dfigueroa11/bibliotecas_autoprestamo_UNAL/carcasa final/Caja 1.0/Captura de pantalla 2022-06-06 223202.png

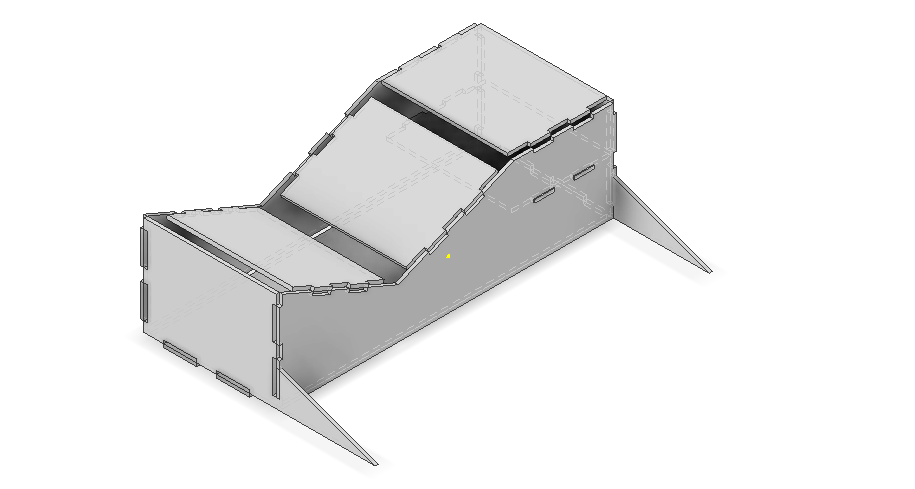
carcasa final/Caja 1.0/Captura de pantalla 2022-06-06 223202.png
