dfigueroa11/bibliotecas_autoprestamo_UNAL/images/autenticación.PNG

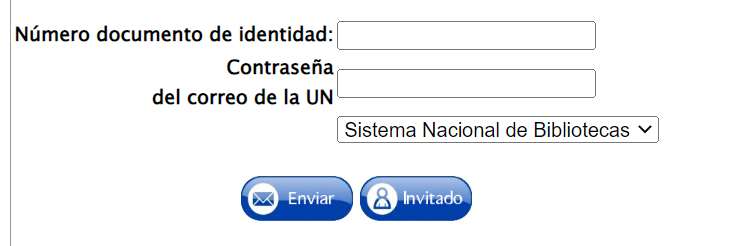
images/autenticación.PNG
