dfigueroa11/bibliotecas_autoprestamo_UNAL/images/autoprestamo.PNG

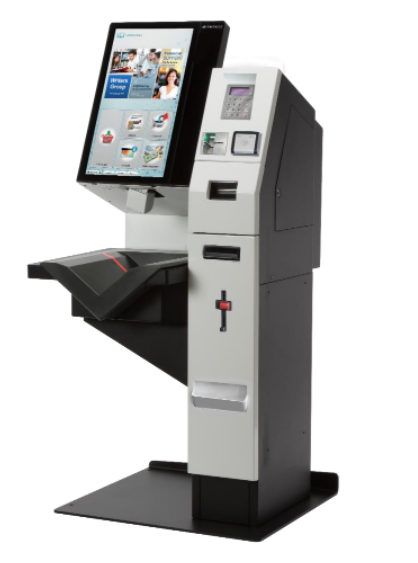
images/autoprestamo.PNG
