dfigueroa11/bibliotecas_autoprestamo_UNAL/images/biblioteca.PNG

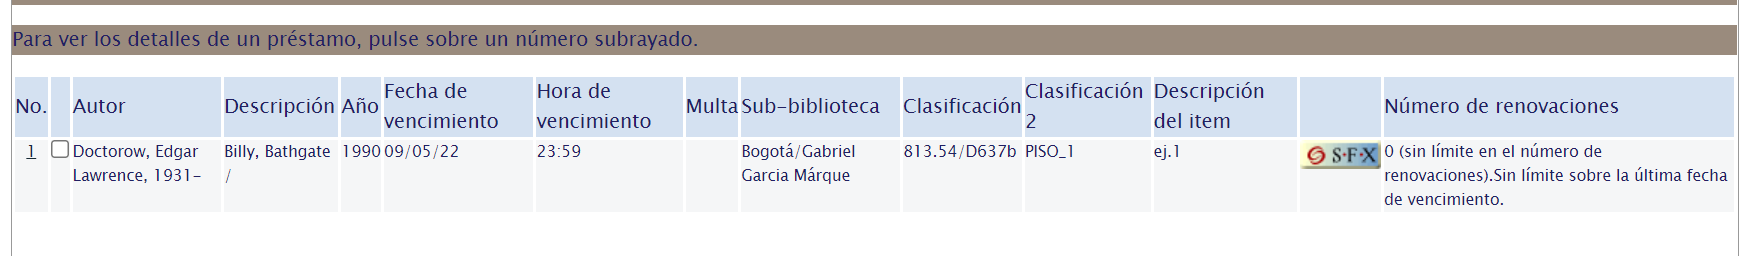
images/biblioteca.PNG
