dfigueroa11/bibliotecas_autoprestamo_UNAL/images/bibliotecas1.jpg

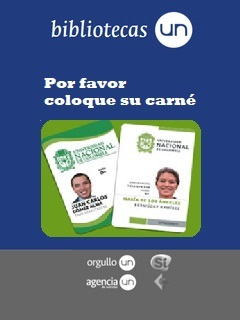
images/bibliotecas1.jpg
