dfigueroa11/bibliotecas_autoprestamo_UNAL/images/bibliotecas2.jpg

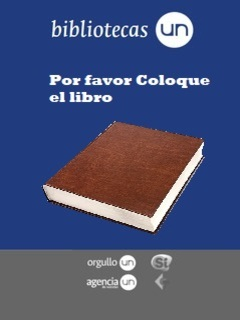
images/bibliotecas2.jpg
