dfigueroa11/bibliotecas_autoprestamo_UNAL/images/bibliotecas3.jpg

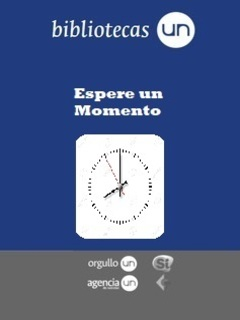
images/bibliotecas3.jpg
