dfigueroa11/bibliotecas_autoprestamo_UNAL/images/bibliotecas4.jpg

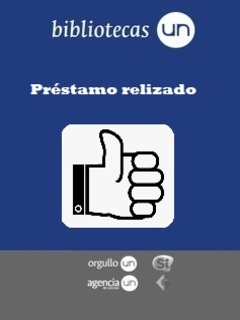
images/bibliotecas4.jpg
