dfigueroa11/bibliotecas_autoprestamo_UNAL/images/carcasa1.jpeg

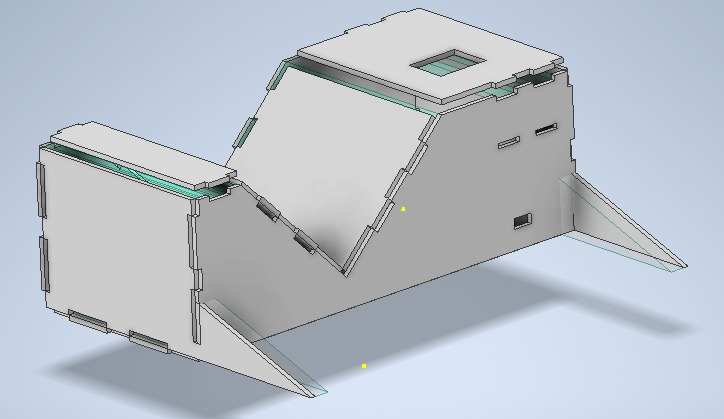
images/carcasa1.jpeg
