dfigueroa11/bibliotecas_autoprestamo_UNAL/images/diagrama_bloques.png

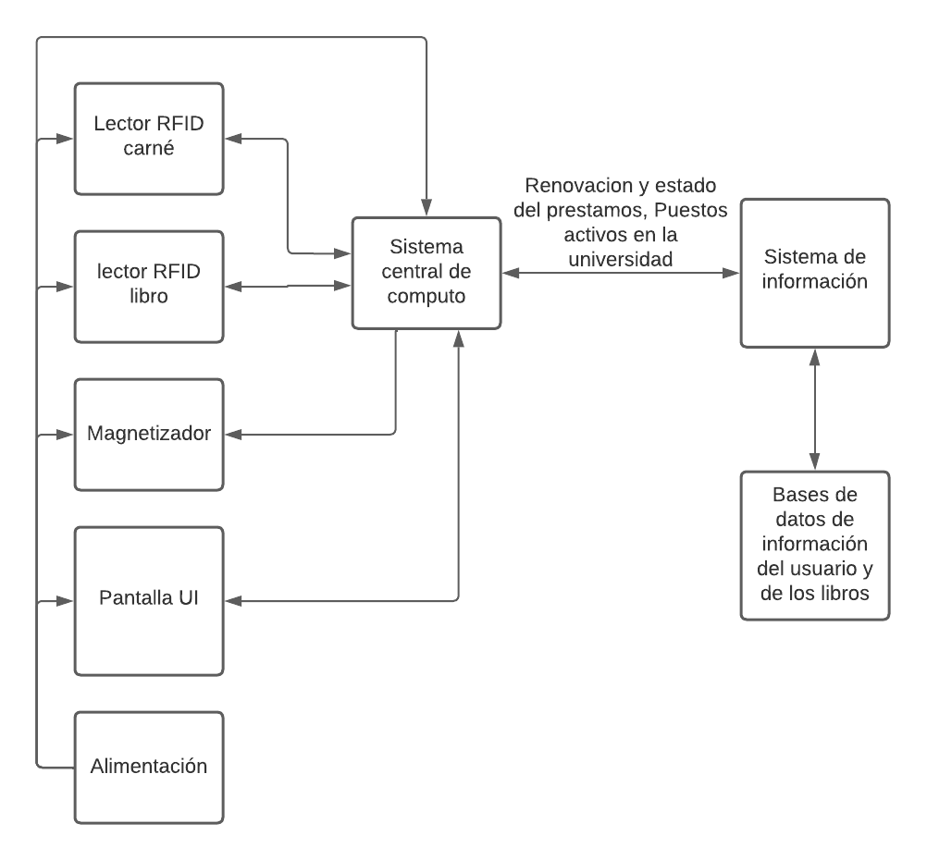
images/diagrama_bloques.png
