dfigueroa11/bibliotecas_autoprestamo_UNAL/images/diagrama_conexiones.png

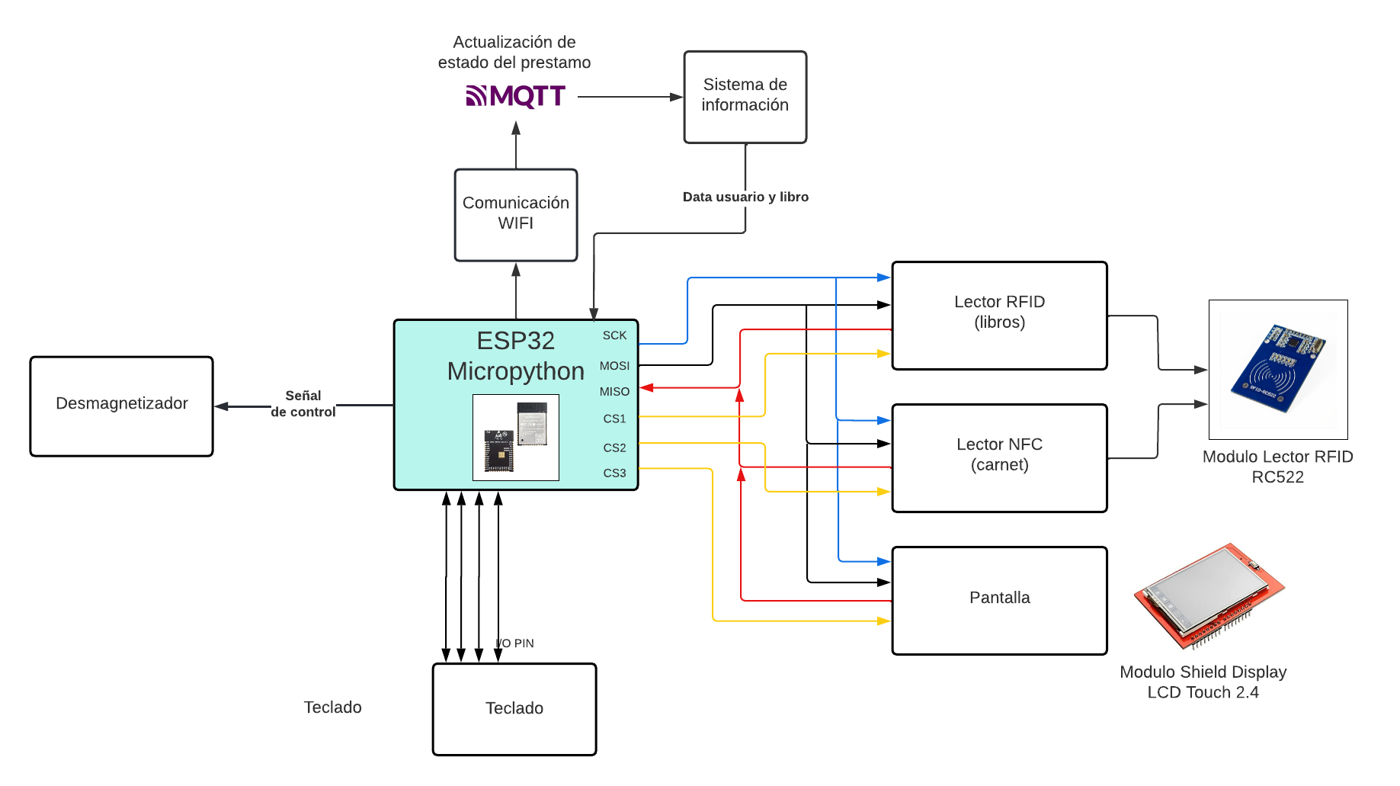
images/diagrama_conexiones.png
