dfigueroa11/bibliotecas_autoprestamo_UNAL/images/diagrama_de_software.jpg

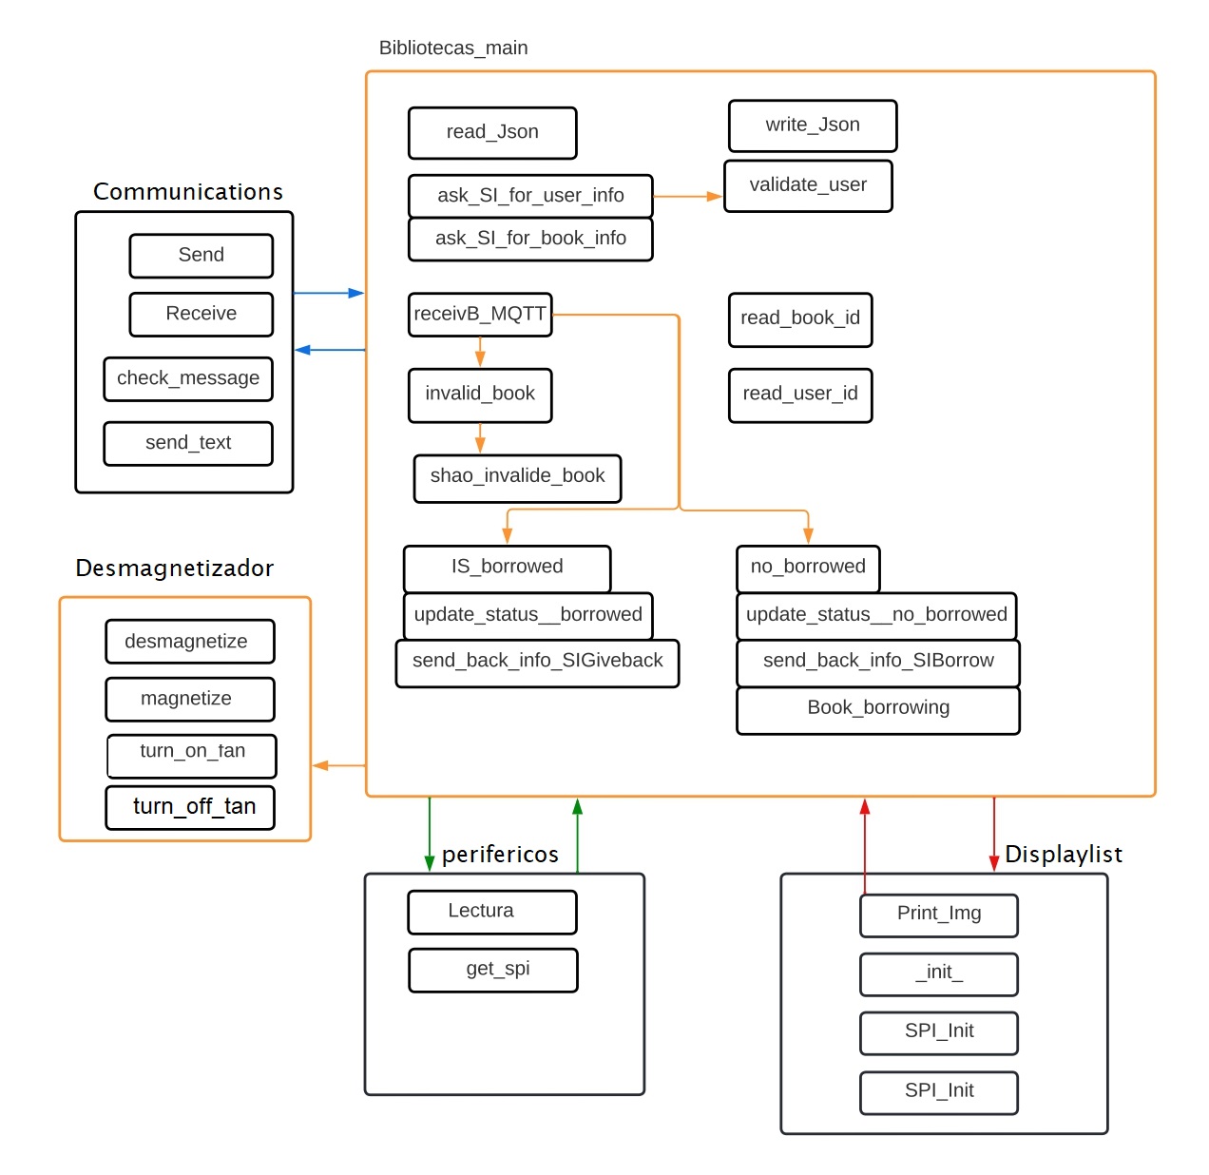
images/diagrama_de_software.jpg
