dfigueroa11/bibliotecas_autoprestamo_UNAL/images/ejemplo_bobinas_desmagnetizador.png

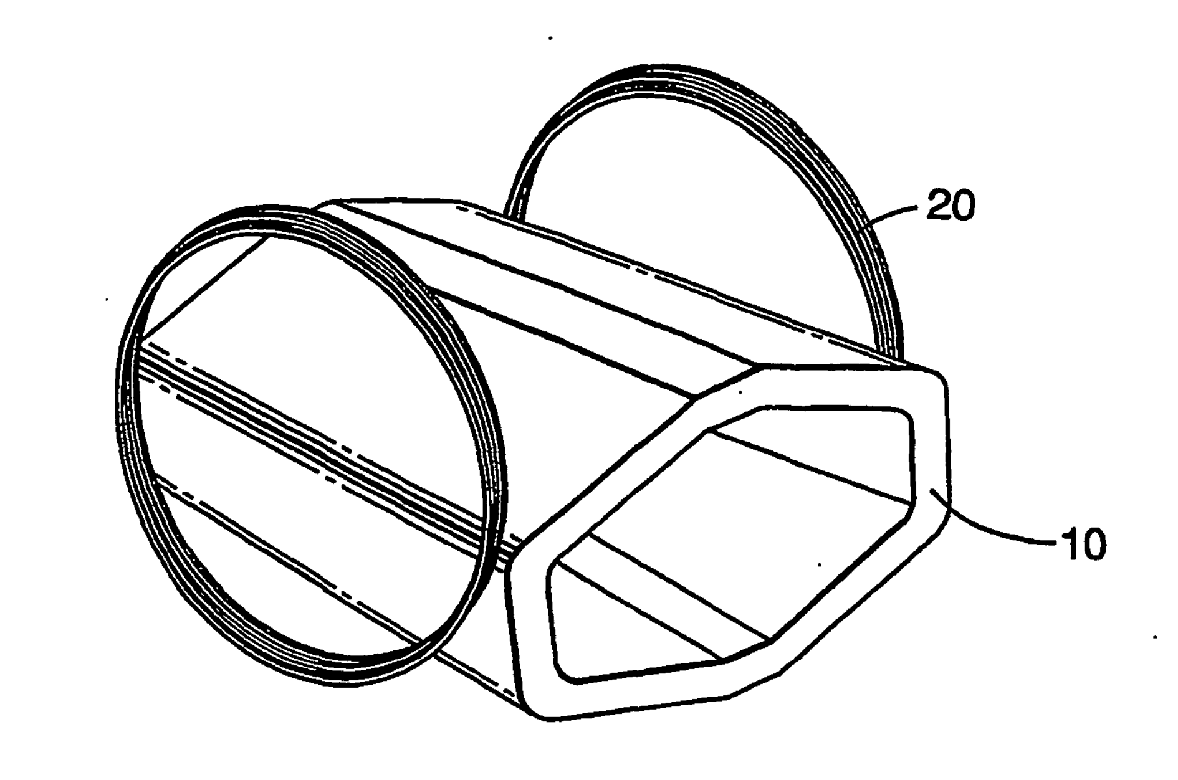
images/ejemplo_bobinas_desmagnetizador.png
