dfigueroa11/bibliotecas_autoprestamo_UNAL/images/ejemplo_circuito_desmagnetizador.png

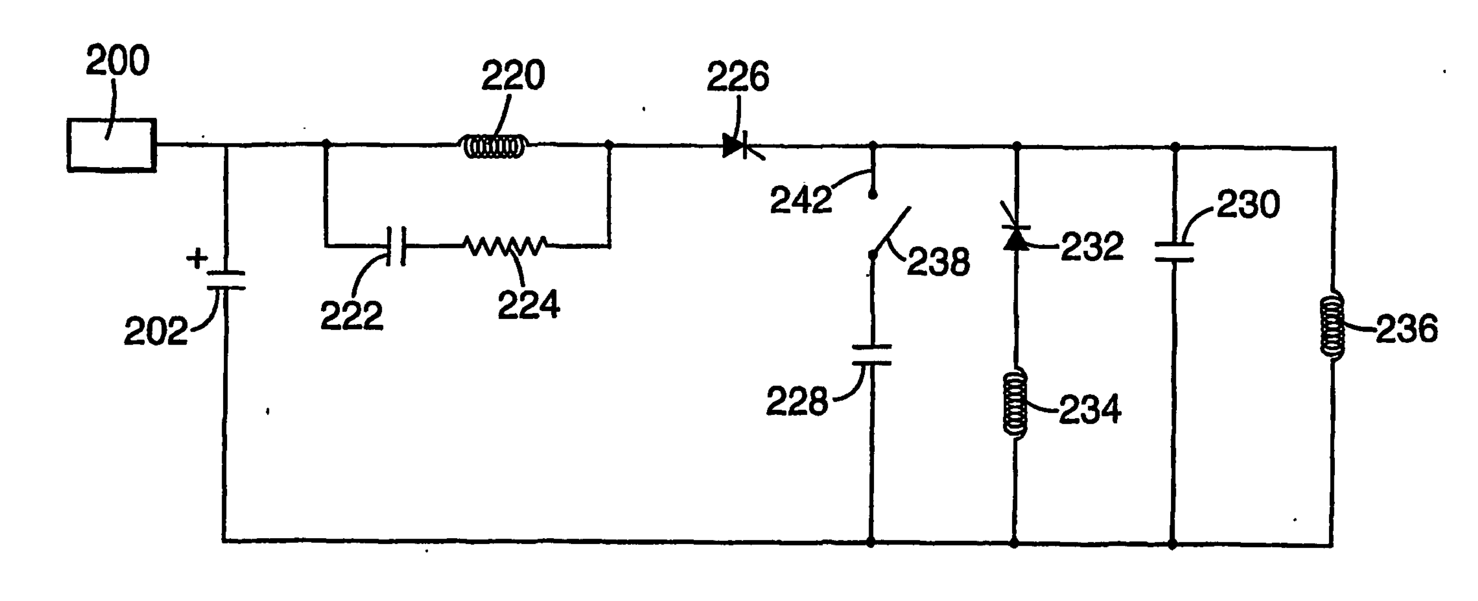
images/ejemplo_circuito_desmagnetizador.png
