dfigueroa11/bibliotecas_autoprestamo_UNAL/images/esquema.PNG

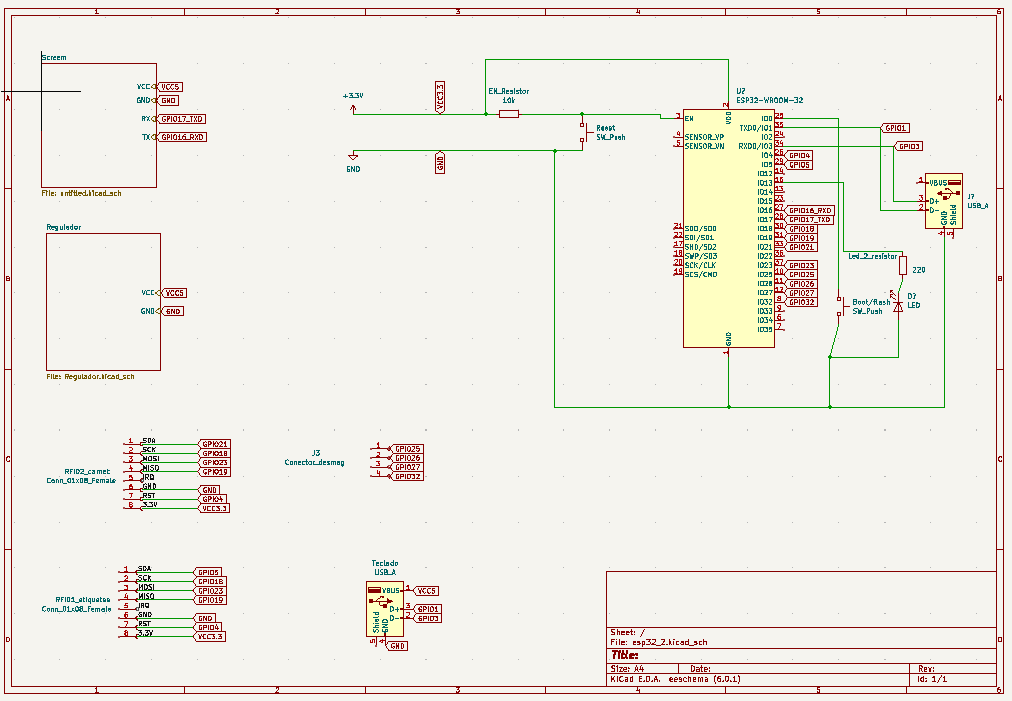
images/esquema.PNG
