dfigueroa11/bibliotecas_autoprestamo_UNAL/images/esquema_esp.PNG

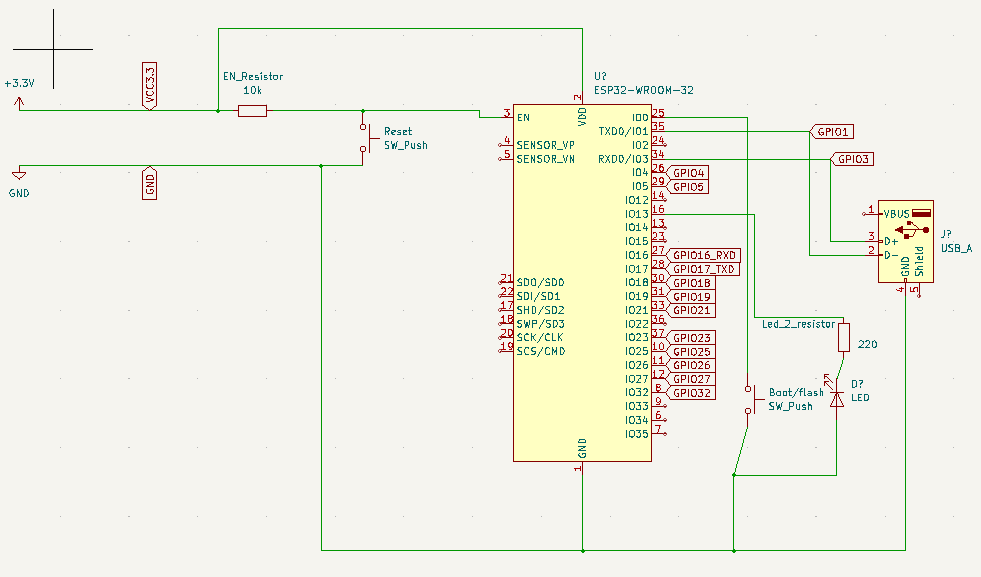
images/esquema_esp.PNG
