dfigueroa11/bibliotecas_autoprestamo_UNAL/images/esquema_fuente.PNG

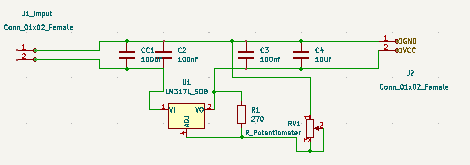
images/esquema_fuente.PNG
