dfigueroa11/bibliotecas_autoprestamo_UNAL/images/esquema_pantalla.PNG

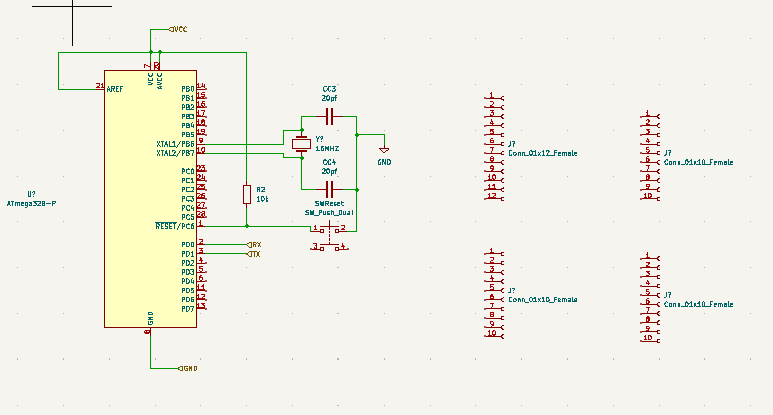
images/esquema_pantalla.PNG
