dfigueroa11/bibliotecas_autoprestamo_UNAL/images/esquema_serial.PNG

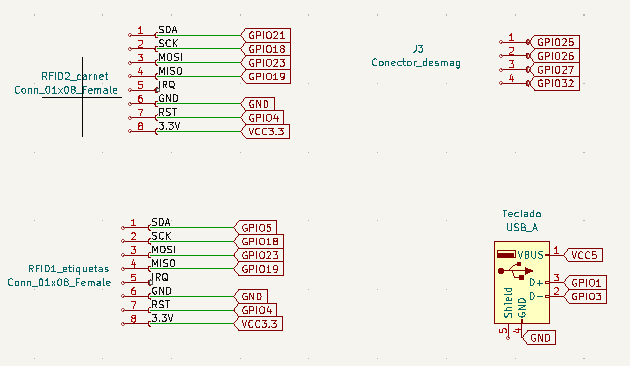
images/esquema_serial.PNG
