dfigueroa11/bibliotecas_autoprestamo_UNAL/images/flujo_bibliotecas.png

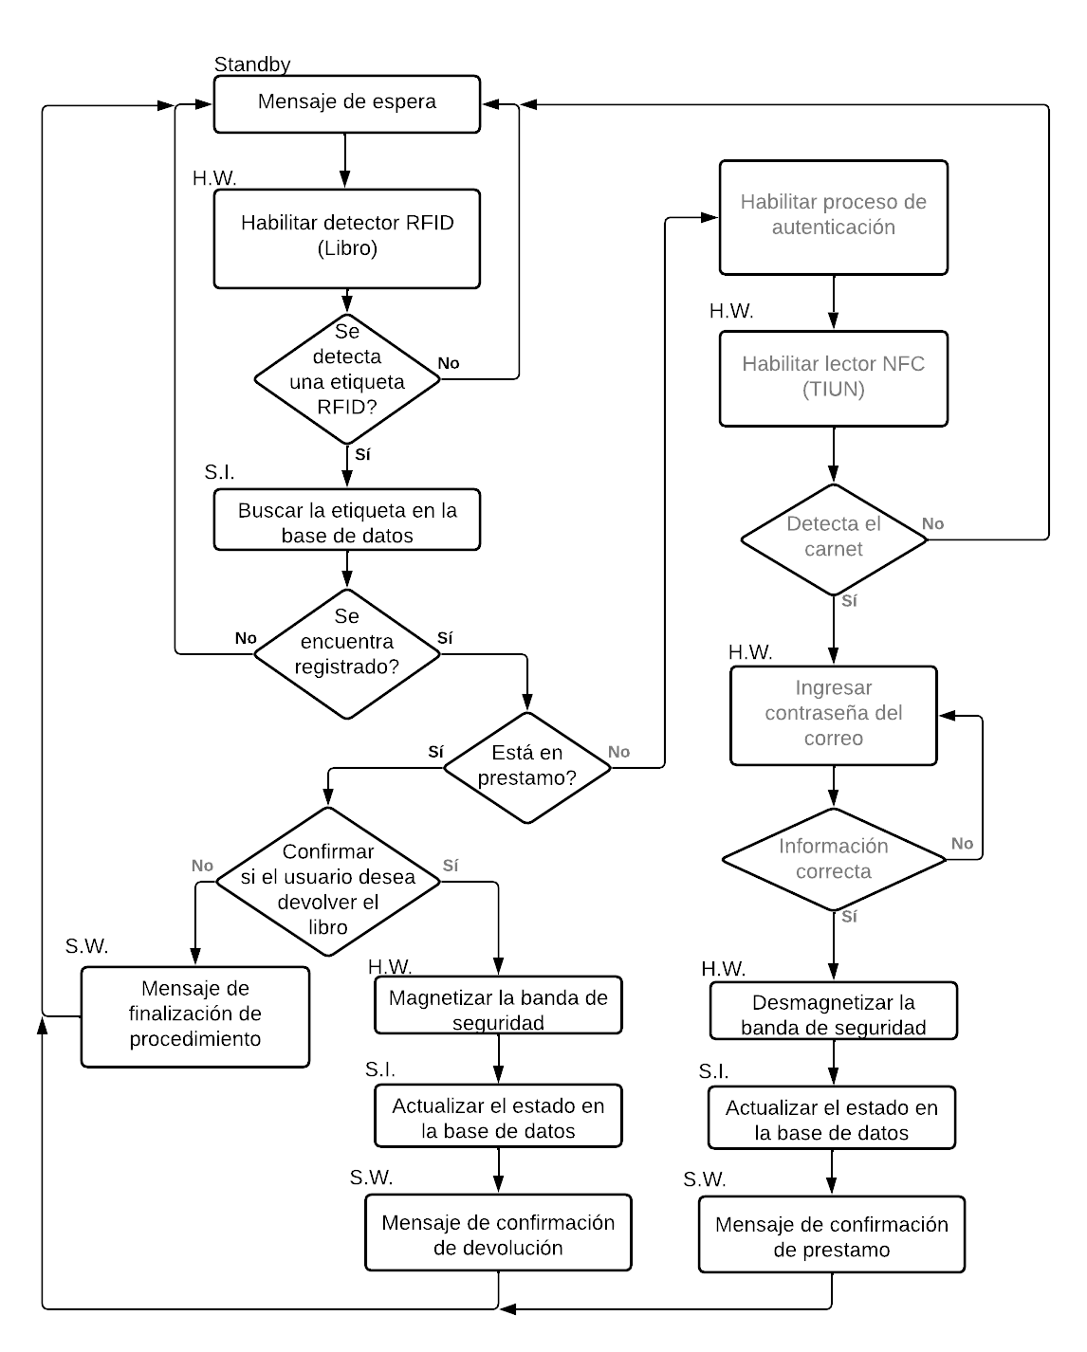
images/flujo_bibliotecas.png
