dfigueroa11/bibliotecas_autoprestamo_UNAL/images/ili9341.jpg

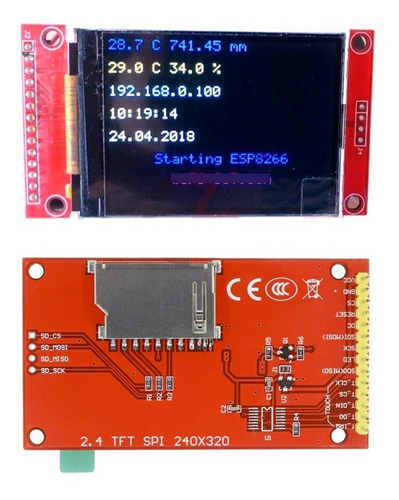
images/ili9341.jpg
