dfigueroa11/bibliotecas_autoprestamo_UNAL/images/keypad.PNG

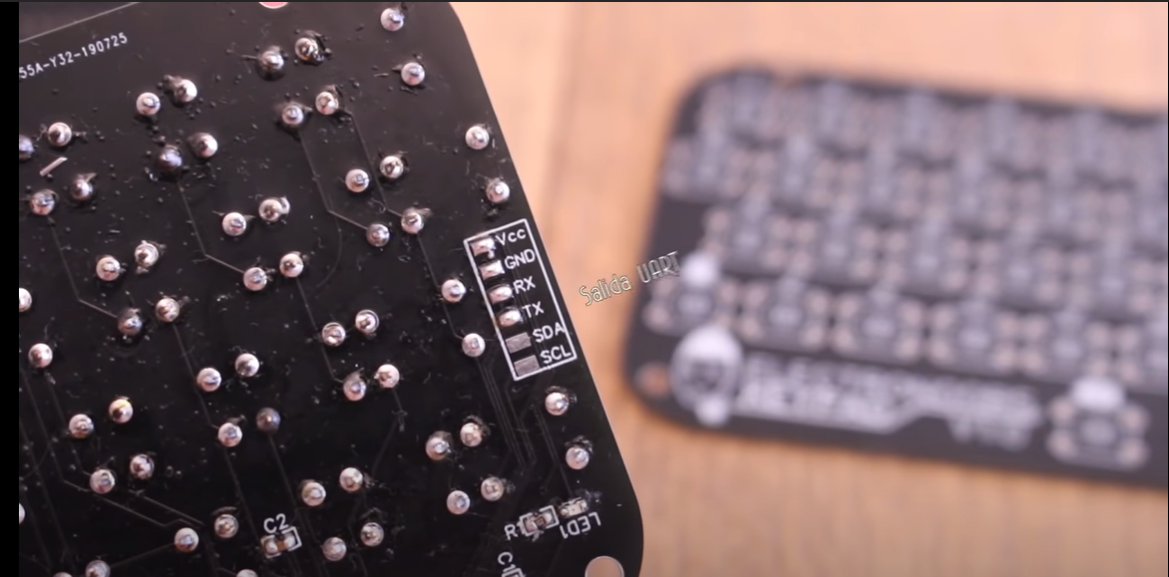
images/keypad.PNG
