dfigueroa11/bibliotecas_autoprestamo_UNAL/images/laboratorio.jpeg

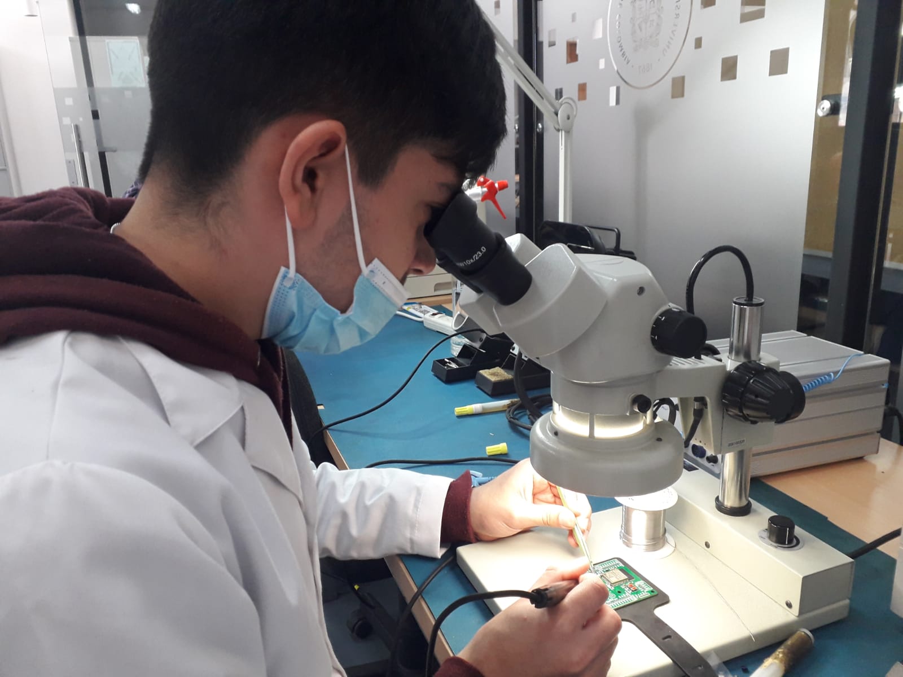
images/laboratorio.jpeg
