dfigueroa11/bibliotecas_autoprestamo_UNAL/images/libro.jpg

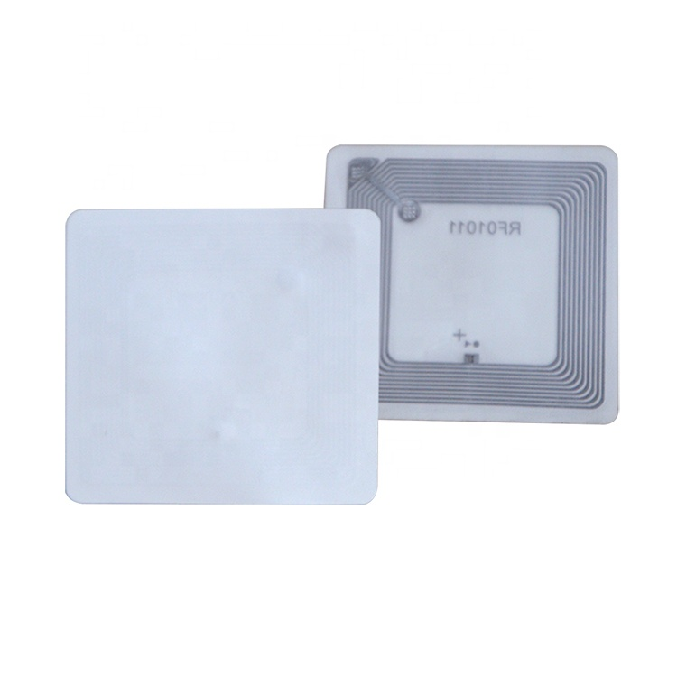
images/libro.jpg
