dfigueroa11/bibliotecas_autoprestamo_UNAL/images/nema.PNG

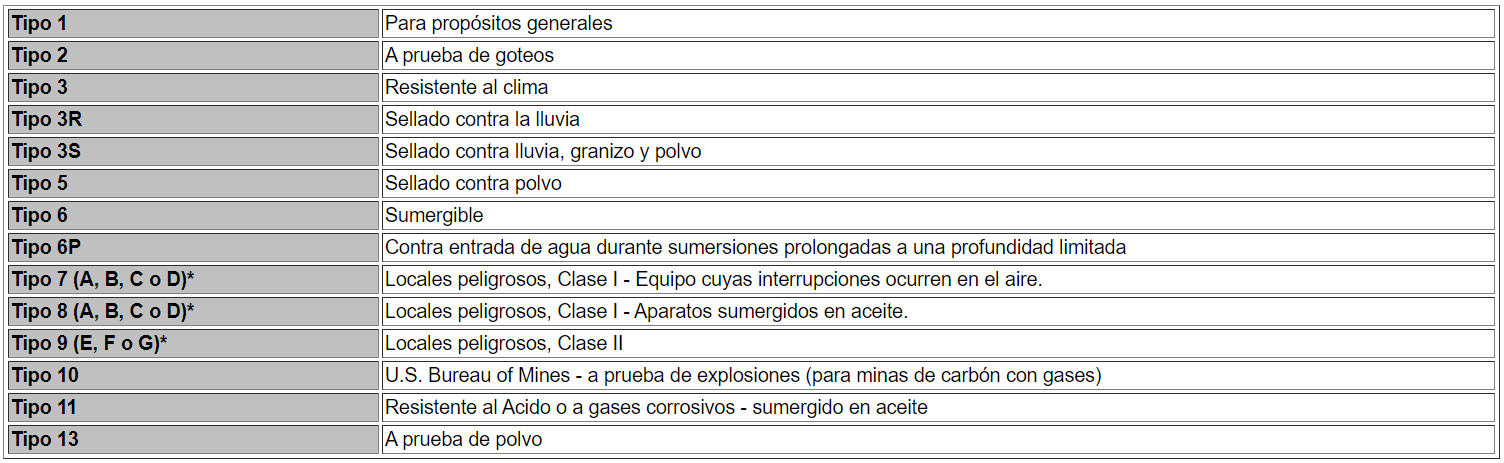
images/nema.PNG
