dfigueroa11/bibliotecas_autoprestamo_UNAL/images/pantalla.jpg

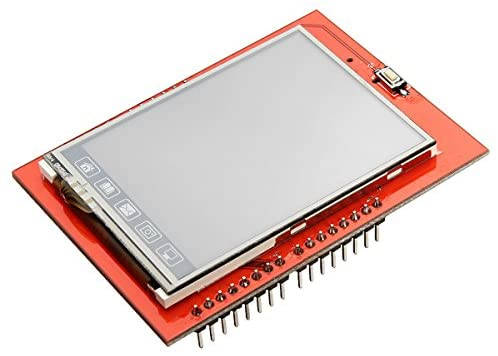
images/pantalla.jpg
