dfigueroa11/bibliotecas_autoprestamo_UNAL/images/pantalla.PNG

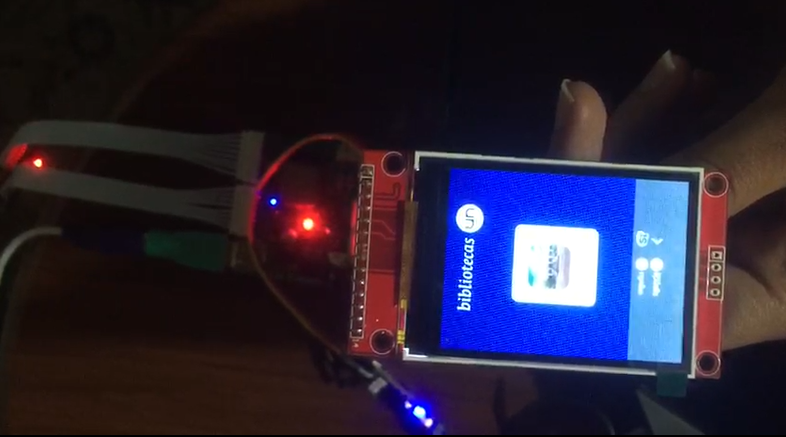
images/pantalla.PNG
