dfigueroa11/bibliotecas_autoprestamo_UNAL/images/pantalla_2.jpeg

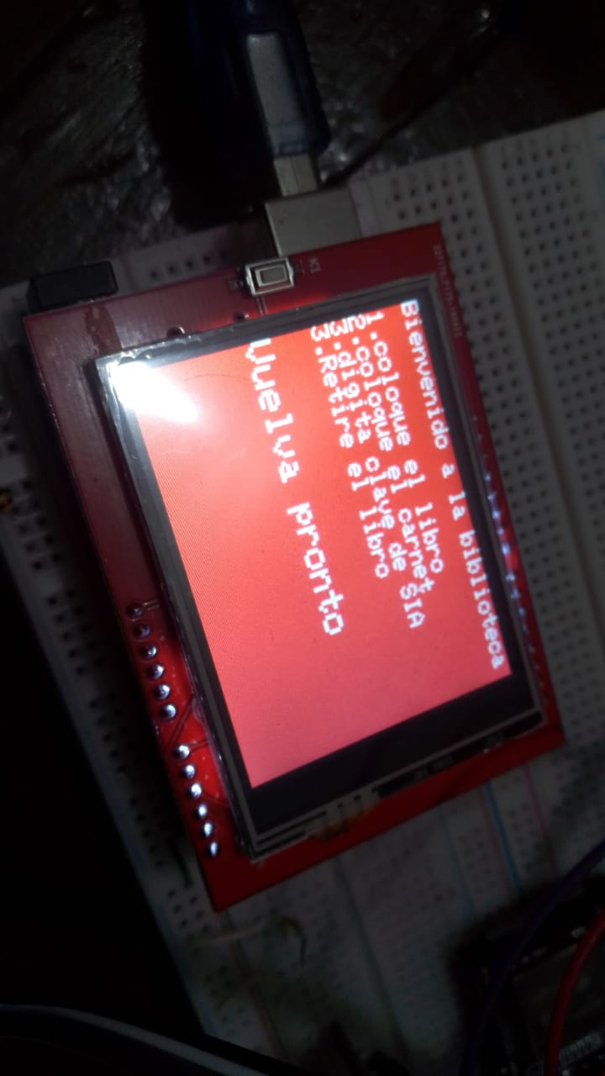
images/pantalla_2.jpeg
