dfigueroa11/bibliotecas_autoprestamo_UNAL/images/rfid_image.PNG

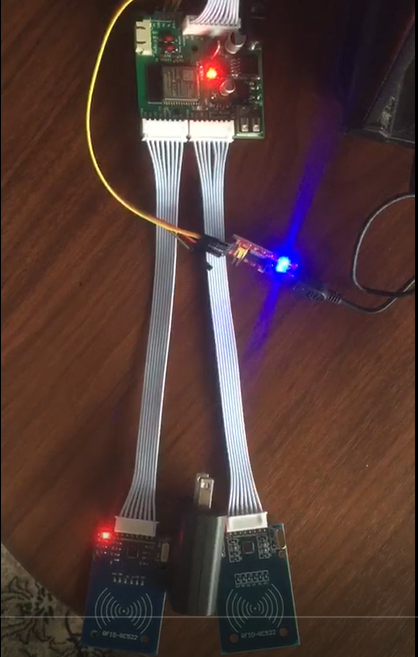
images/rfid_image.PNG
