dfigueroa11/bibliotecas_autoprestamo_UNAL/images/rfidcode.PNG

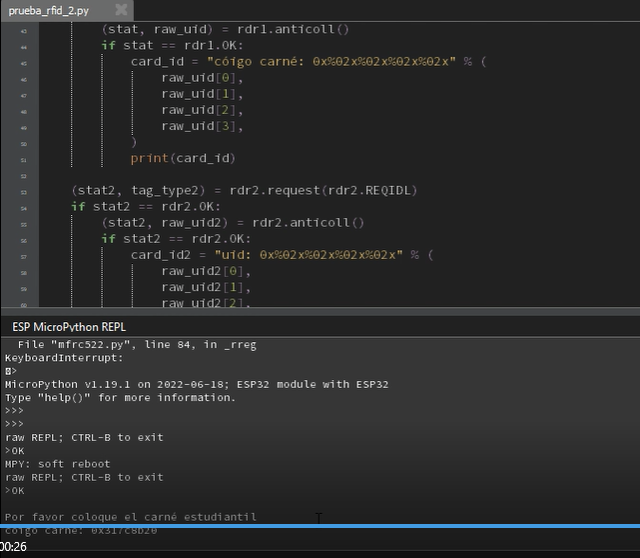
images/rfidcode.PNG
