dfigueroa11/bibliotecas_autoprestamo_UNAL/images/SI.jpg

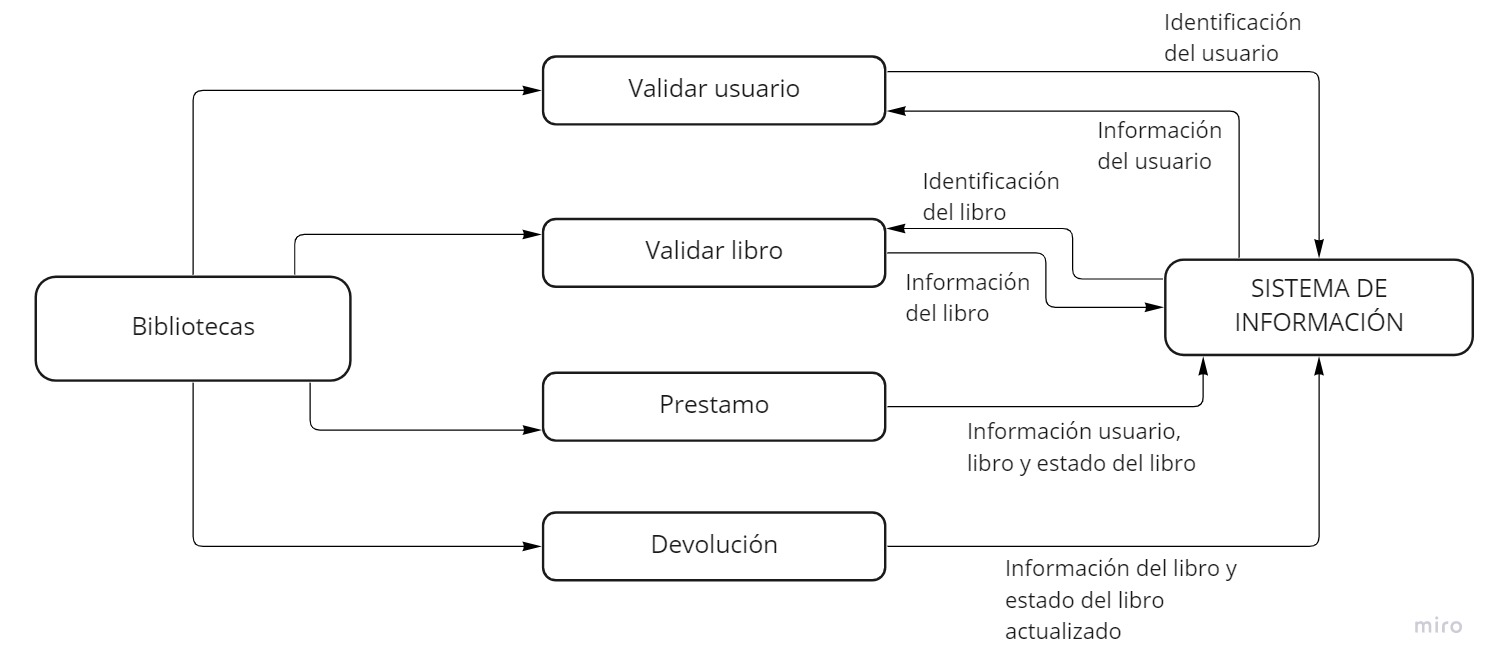
images/SI.jpg
