dfigueroa11/bibliotecas_autoprestamo_UNAL/images/slb01_2.jpg

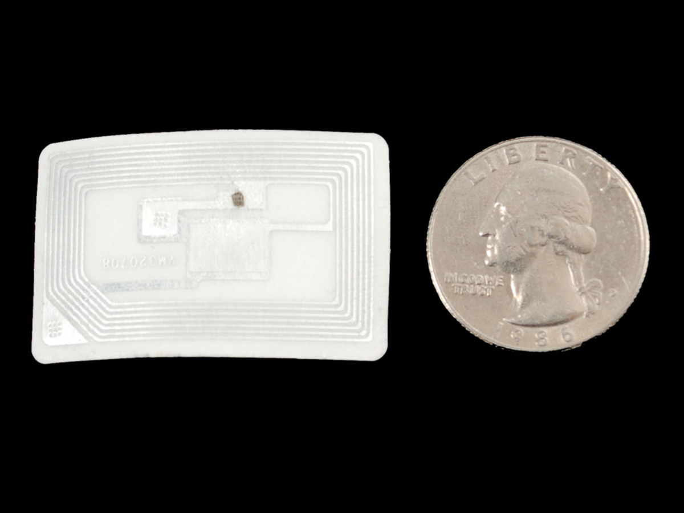
images/slb01_2.jpg
