dfigueroa11/bibliotecas_autoprestamo_UNAL/images/teclado_ps_2.PNG

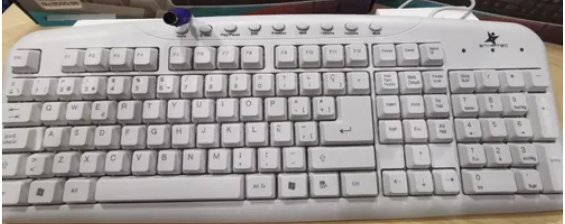
images/teclado_ps_2.PNG
