dfigueroa11/bibliotecas_autoprestamo_UNAL/images/USB.PNG

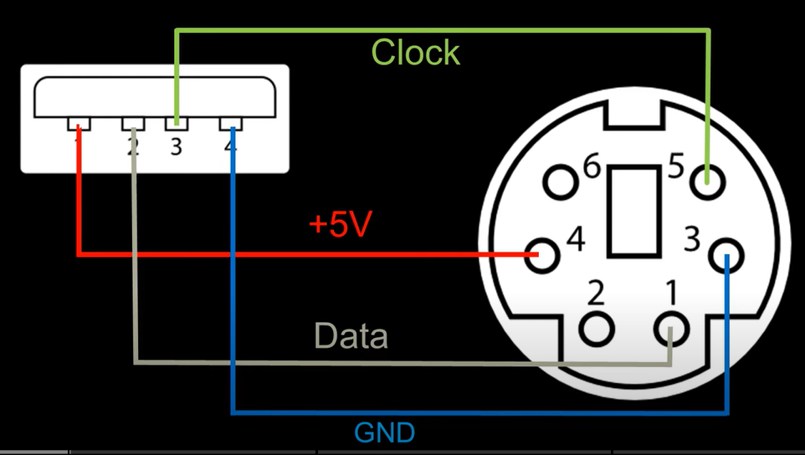
images/USB.PNG
