dfigueroa11/bibliotecas_autoprestamo_UNAL/Sensibilizador_PCB/BookSensitizer.png

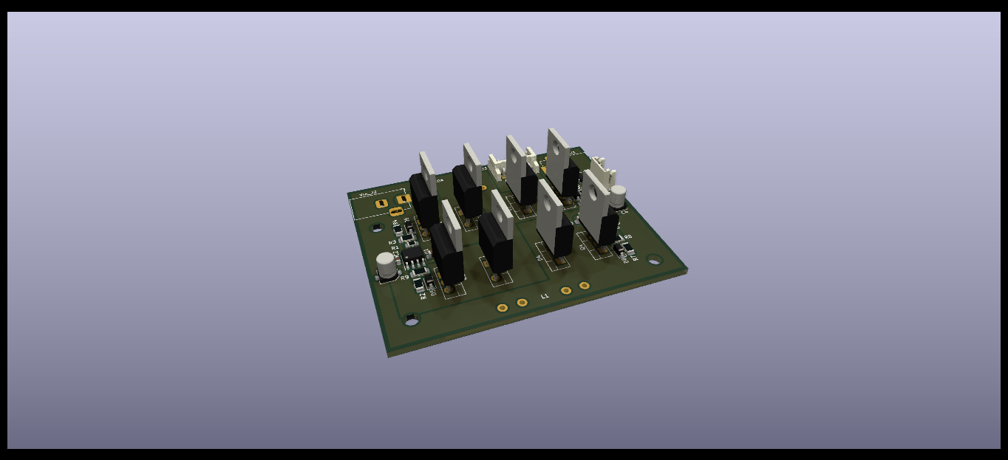
Sensibilizador_PCB/BookSensitizer.png
