dfigueroa11/bibliotecas_autoprestamo_UNAL/Sensibilizador_PCB/Inferior.png

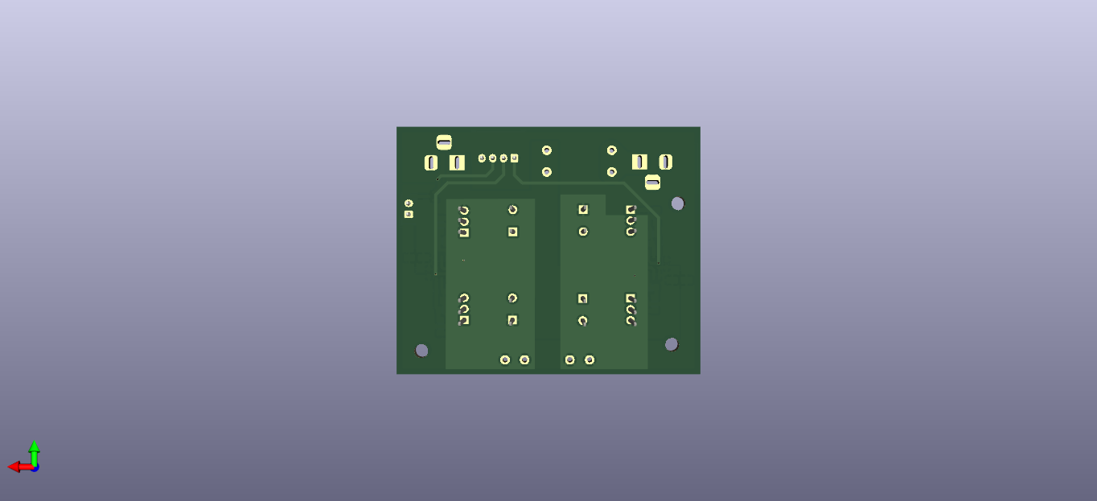
Sensibilizador_PCB/Inferior.png
