dfigueroa11/bibliotecas_autoprestamo_UNAL/carcasa final/Caja 1.0/Ensamble caja.png

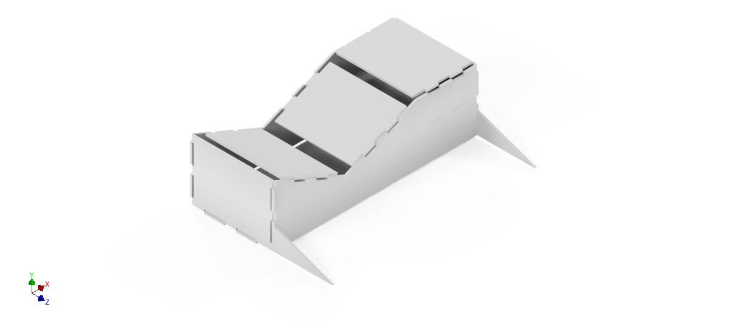
carcasa final/Caja 1.0/Ensamble caja.png
