dfigueroa11/bibliotecas_autoprestamo_UNAL/images/bibliotecas_prueba.PNG

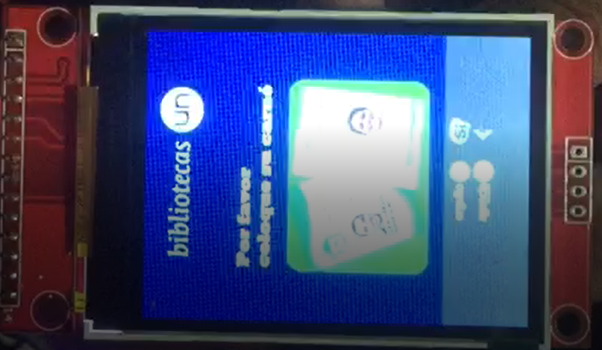
images/bibliotecas_prueba.PNG
