dfigueroa11/bibliotecas_autoprestamo_UNAL/images/teclado_ps_2_prueba.PNG

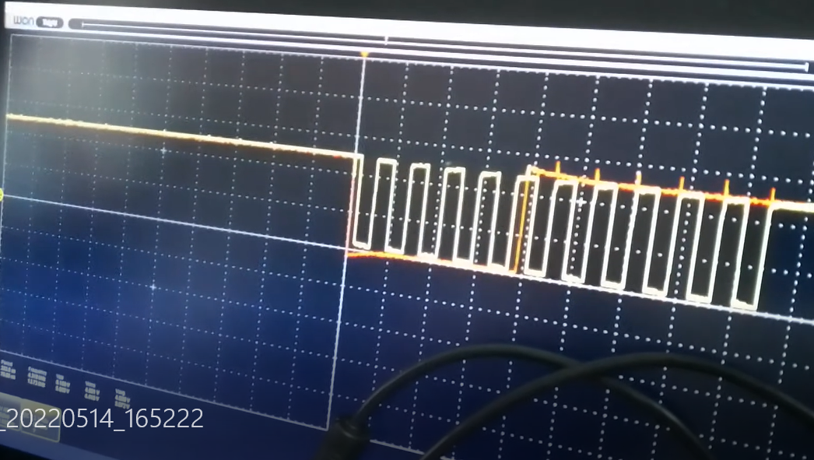
images/teclado_ps_2_prueba.PNG
